ahmetakif/TinyBot-Legged/SolidWorks/leg-mirrored.SLDPRT

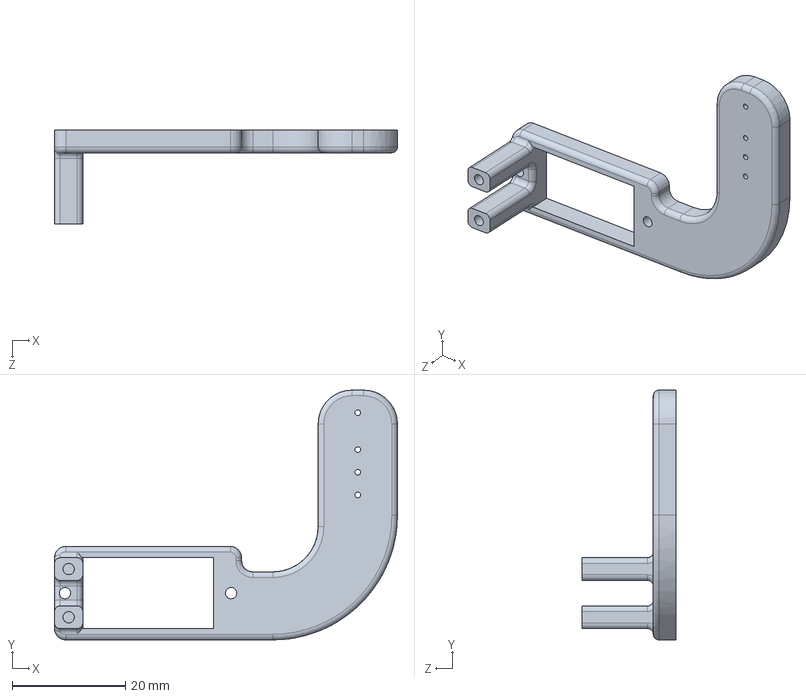
[picture p15: CAD file, 2020-11-15]
SolidWorks/leg-mirrored.SLDPRT
60.5 x 44.1 x 16.6 mm
