ahmetakif/TinyBot-Legged/SolidWorks/TopC.SLDPRT

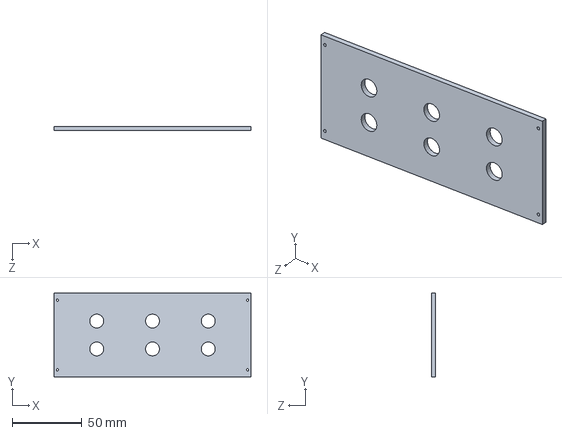
[picture p16: CAD file, 2020-11-15]
SolidWorks/TopC.SLDPRT
141.3 x 60.0 x 3.00 mm
